catrax/kilter/panel/pcb/.svg2shenzhen-cache/images/F.Cu_g249.png

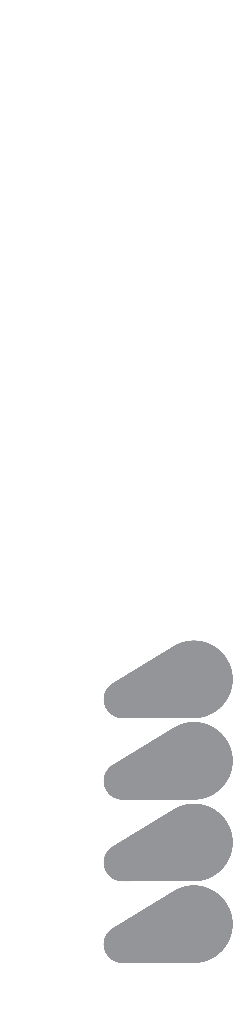
panel/pcb/.svg2shenzhen-cache/images/F.Cu_g249.png
